jorgeg922/Robotic-Hand/3D Hand Model/Flexy-Hand_2/8.stl

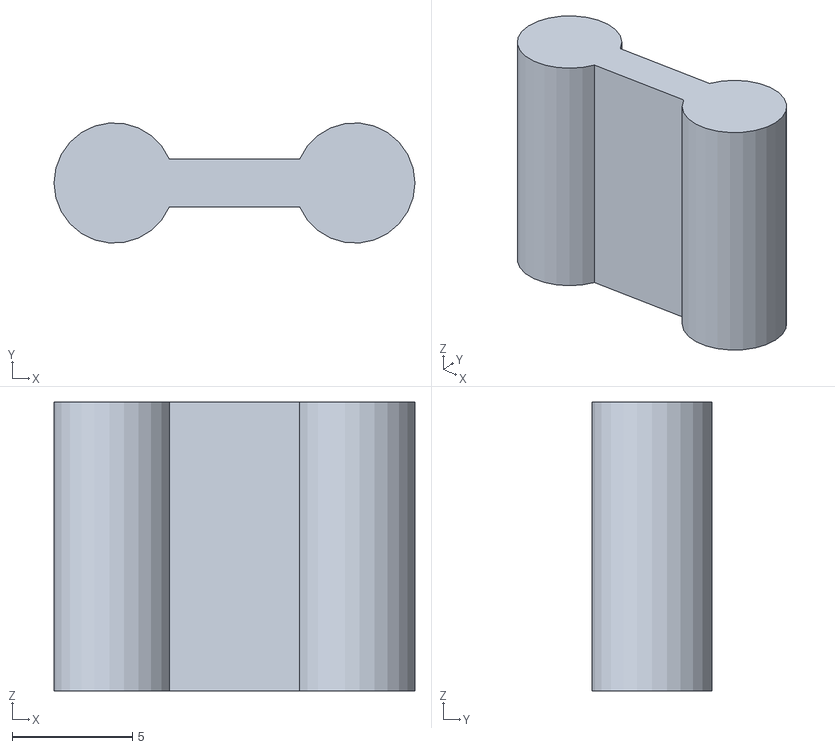
[picture p27: CAD file, 2017-09-14]
3D Hand Model/Flexy-Hand_2/8.stl
15.0 x 4.98 x 12.0
