jorgeg922/Robotic-Hand/3D Hand Model/Flexy-Hand_2/LH_Finger_Plate.stl

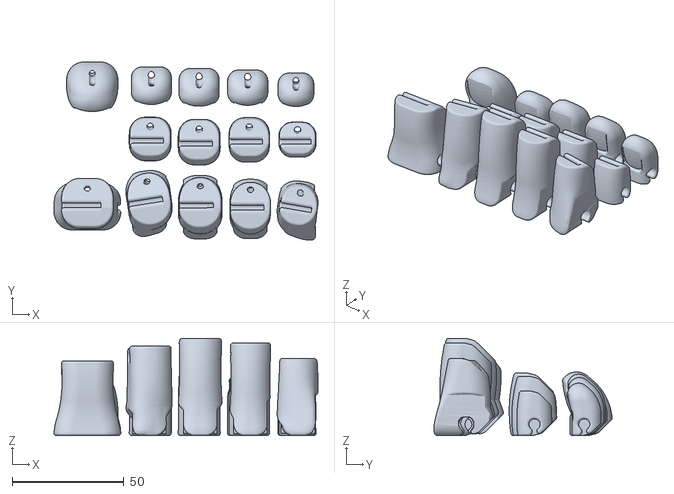
[picture p28: CAD file, 2017-09-14]
3D Hand Model/Flexy-Hand_2/LH_Finger_Plate.stl
118.3 x 79.9 x 43.5
