jorgeg922/Robotic-Hand/3D Hand Model/Flexy-Hand_2/Gauntlet_-_Long.stl

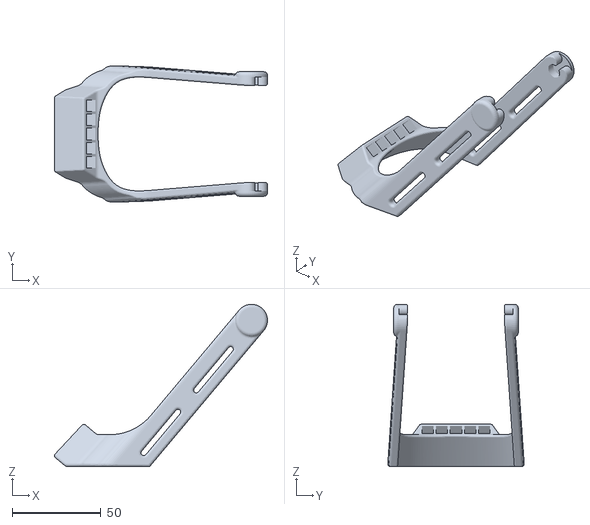
[picture p29: CAD file, 2017-09-14]
3D Hand Model/Flexy-Hand_2/Gauntlet_-_Long.stl
119.7 x 76.7 x 91.2
