jorgeg922/Robotic-Hand/3D Hand Model/Flexy-Hand_2/FFX_-_Flexy-Hinge_Wrist.stl

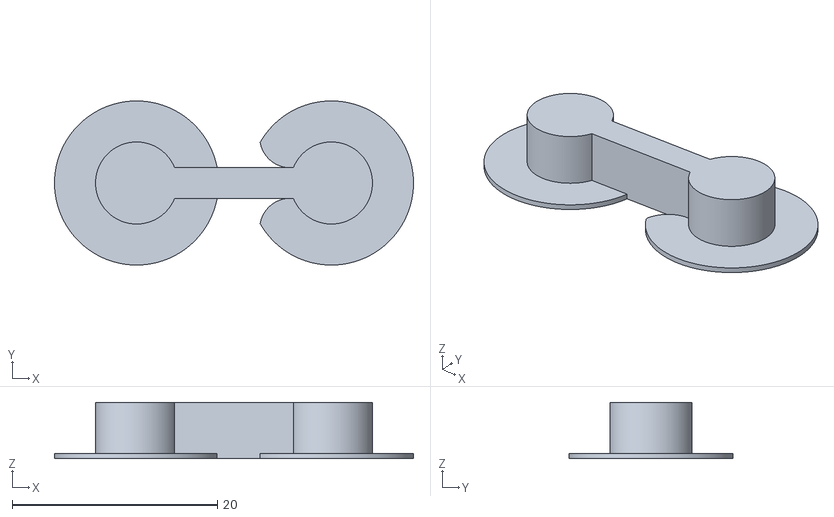
[picture p30: CAD file, 2017-09-14]
3D Hand Model/Flexy-Hand_2/FFX_-_Flexy-Hinge_Wrist.stl
35.0 x 16.0 x 5.50
