jorgeg922/Robotic-Hand/3D Hand Model/Flexy-Hand_2/RH_Hand_Body_-_Wider_Wrist_-_No_Thumb.stl

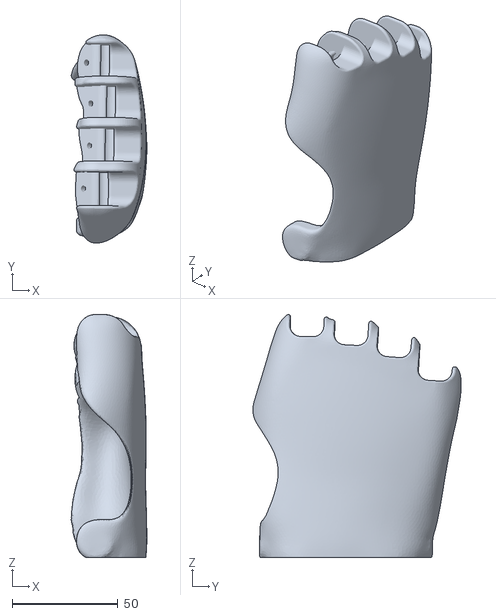
[picture p31: CAD file, 2017-09-14]
3D Hand Model/Flexy-Hand_2/RH_Hand_Body_-_Wider_Wrist_-_No_Thumb.stl
35.7 x 98.3 x 114.7
