jorgeg922/Robotic-Hand/3D Hand Model/Flexy-Hand_2/FFX_-_Finger_Hinge_Plate.stl

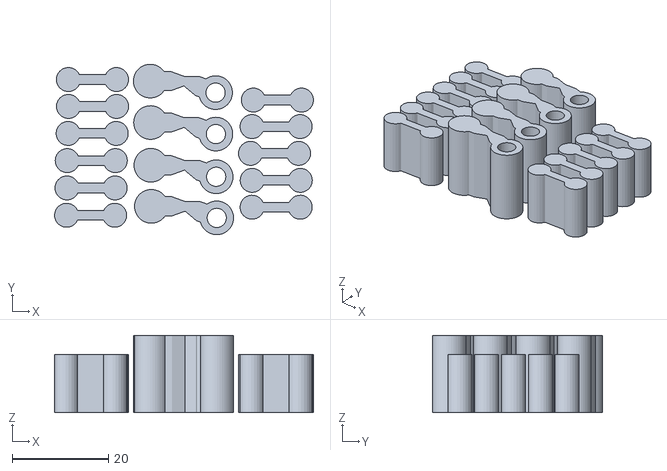
[picture p32: CAD file, 2017-09-14]
3D Hand Model/Flexy-Hand_2/FFX_-_Finger_Hinge_Plate.stl
53.8 x 35.4 x 16.0
