jorgeg922/Robotic-Hand/3D Hand Model/Flexy-Hand_2/Gauntlet_-_Short_Wider_Wrist.stl

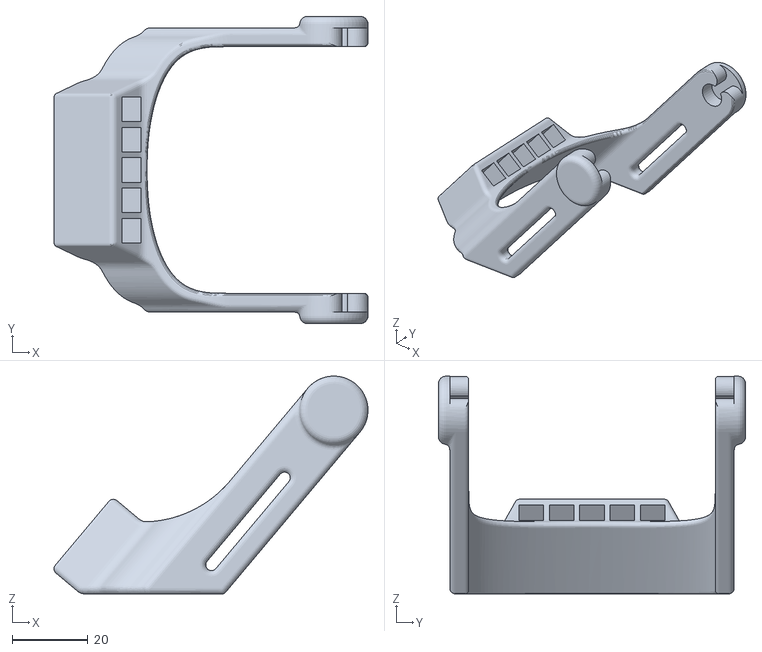
[picture p33: CAD file, 2017-09-14]
3D Hand Model/Flexy-Hand_2/Gauntlet_-_Short_Wider_Wrist.stl
82.8 x 81.0 x 57.4
